yacchin1205/puchi-pix/puchi_pix_esp32/1_28inch_LCD_Module_-_Waveshare_Wiki.png

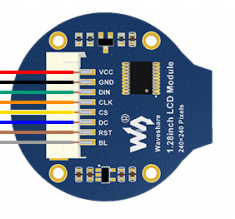
puchi_pix_esp32/1_28inch_LCD_Module_-_Waveshare_Wiki.png
