yacchin1205/puchi-pix/puchi_pix_esp32/1_28inch_LCD_Module_SchDoc_pdf.png

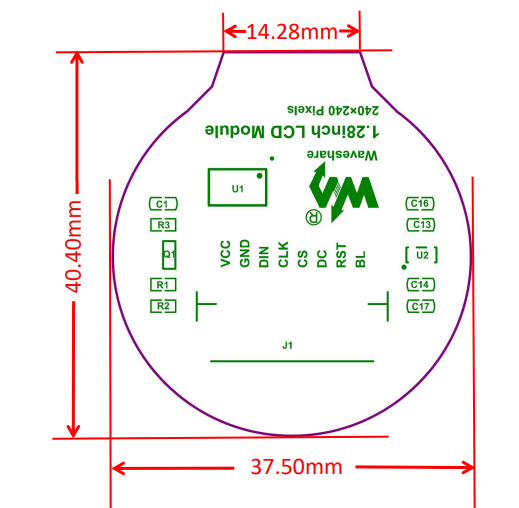
puchi_pix_esp32/1_28inch_LCD_Module_SchDoc_pdf.png
